DrMikeG/pico-macro-keyboard2/KeyPad/hid-simple/hid-keys-simple.py

# SPDX-FileCopyrightText: 2021 Sandy Macdonald
#
# SPDX-License-Identifier: MIT

# A simple example of how to set up a keymap and HID keyboard on Keybow 2040.

# You'll need to connect Keybow 2040 to a computer, as you would with a regular
# USB keyboard.

# Drop the `pmk` folder
# into your `lib` folder on your `CIRCUITPY` drive.

# NOTE! Requires the adafruit_hid CircuitPython library also!

from pmk import PMK
#from pmk.platform.keybow2040 import Keybow2040 as Hardware          # for Keybow 2040
from pmk.platform.rgbkeypadbase import RGBKeypadBase as Hardware  # for Pico RGB Keypad Base

import usb_hid
from adafruit_hid.keyboard import Keyboard
from adafruit_hid.keyboard_layout_us import KeyboardLayoutUS
from adafruit_hid.keycode import Keycode

# Set up Keybow
keybow = PMK(Hardware())
keys = keybow.keys

# Set up the keyboard and layout
keyboard = Keyboard(usb_hid.devices)
layout = KeyboardLayoutUS(keyboard)

# A map of keycodes that will be mapped sequentially to each of the keys, 0-15
keymap =    [Keycode.ZERO,
             Keycode.ONE,
             Keycode.TWO,
             Keycode.THREE,
             Keycode.FOUR,
             Keycode.FIVE,
             Keycode.SIX,
             Keycode.SEVEN,
             Keycode.EIGHT,
             Keycode.NINE,
             Keycode.A,
             Keycode.B,
             Keycode.C,
             Keycode.D,
             Keycode.E,
             Keycode.F]

# The colour to set the keys when pressed, yellow.
rgb = (255, 255, 0)

# Attach handler functions to all of the keys
for key in keys:
    # A press handler that sends the keycode and turns on the LED
    @keybow.on_press(key)
    def press_handler(key):
        keycode = keymap[key.number]
        keyboard.send(keycode)
        key.set_led(*rgb)

    # A release handler that turns off the LED
    @keybow.on_release(key)
    def release_handler(key):
        key.led_off()

while True:
    # Always remember to call keybow.update()!
    keybow.update()
